MaxDYi/eElements/2.Firmware/eElements/Drivers/PWR/PWR.c

/*
 * @FilePath: \eElements\Drivers\PWR\PWR.c
 * @Author: MaxDYi
 * @Date: 2024-04-07 18:13:32
 * @LastEditors: MaxDYi
 * @LastEditTime: 2024-04-15 11:42:31
 * @Description:能耗管理相关的库函数
 */

#include "PWR.h"

 /**
  * @description: 关闭RTC唤醒定时器
  * @return {*}
  */
void PWR_CLK_Disable(void)
{
    RTC_HandleTypeDef RTCHandle;
    HAL_RTCEx_DeactivateWakeUpTimer(&RTCHandle);
}

/**
 * @description: 关闭GPIOA
 * @return {*}
 */
void PWR_DisableGPIOA(void) {
    __HAL_RCC_GPIOA_CLK_ENABLE();
    GPIO_InitTypeDef GPIO_InitStructure = { 0 };
    GPIO_InitStructure.Pin &= (~KEY_Pin);
    GPIO_InitStructure.Mode = GPIO_MODE_ANALOG;
    GPIO_InitStructure.Pull = GPIO_NOPULL;
    HAL_GPIO_Init(GPIOA , &GPIO_InitStructure);
    //__HAL_RCC_GPIOA_CLK_DISABLE();
}

/**
 * @description: 关闭GPIOB
 * @return {*}
 */
void PWR_DisableGPIOB(void) {
    __HAL_RCC_GPIOB_CLK_ENABLE();
    GPIO_InitTypeDef GPIO_InitStructure = { 0 };
    GPIO_InitStructure.Pin = GPIO_PIN_All;
    GPIO_InitStructure.Mode = GPIO_MODE_ANALOG;
    GPIO_InitStructure.Pull = GPIO_NOPULL;
    HAL_GPIO_Init(GPIOB , &GPIO_InitStructure);
    __HAL_RCC_GPIOB_CLK_DISABLE();
}

/**
 * @description: 关闭GPIOC
 * @return {*}
 */
void PWR_DisableGPIOC(void) {
    __HAL_RCC_GPIOC_CLK_ENABLE();
    GPIO_InitTypeDef GPIO_InitStructure = { 0 };
    GPIO_InitStructure.Pin &= (~PWR_LDO_Pin);
    GPIO_InitStructure.Mode = GPIO_MODE_ANALOG;
    GPIO_InitStructure.Pull = GPIO_NOPULL;
    HAL_GPIO_Init(GPIOC , &GPIO_InitStructure);
    //__HAL_RCC_GPIOC_CLK_DISABLE();
}

/**
 * @description: 关闭GPIOH
 * @return {*}
 */
void PWR_DisableGPIOH(void) {
    __HAL_RCC_GPIOH_CLK_ENABLE();
    GPIO_InitTypeDef GPIO_InitStructure = { 0 };
    GPIO_InitStructure.Pin = GPIO_PIN_All;
    GPIO_InitStructure.Mode = GPIO_MODE_ANALOG;
    GPIO_InitStructure.Pull = GPIO_NOPULL;
    HAL_GPIO_Init(GPIOA , &GPIO_InitStructure);
    __HAL_RCC_GPIOH_CLK_DISABLE();
}

/**
 * @description: 进入STOP2低功耗模式
 * @param {uint16_t} stopTime
 * @return {*}
 */
void PWR_EnterStop2Mode(uint16_t stopTime)
{
    HAL_SPI_DeInit(&hspi1);
    HAL_UART_DeInit(&huart1);
    HAL_ADC_DeInit(&hadc1);
    HAL_OPAMP_DeInit(&hopamp1);

    PWR_DisableGPIOA();
    PWR_DisableGPIOB();
    PWR_DisableGPIOC();
    PWR_DisableGPIOH();

    LED_GREEN_GPIO_Deinit();

    WKUP_Init();

    __HAL_RCC_PWR_CLK_ENABLE();
    __HAL_PWR_CLEAR_FLAG(PWR_FLAG_WU);
    __HAL_RCC_WAKEUPSTOP_CLK_CONFIG(RCC_STOP_WAKEUPCLOCK_MSI);
    HAL_RTCEx_DeactivateWakeUpTimer(&hrtc);
    HAL_RTCEx_SetWakeUpTimer_IT(&hrtc , stopTime , RTC_WAKEUPCLOCK_RTCCLK_DIV16);

    HAL_SuspendTick();

    HAL_PWREx_EnterSTOP2Mode(PWR_STOPENTRY_WFI);
}

/**
 * @description:退出STOP2低功耗模式
 * @return {*}
 */
void PWR_ExitStop2Mode(void)
{
    HAL_ResumeTick();
    SystemClock_Config();
    WKUP_Deinit();
    KEY_GPIO_Init();
    HAL_PWR_DisableWakeUpPin(PWR_WAKEUP_PIN4);
    MX_USART1_UART_Init();
    printf("WAKE UP\r\n");
    HAL_UART_DeInit(&huart1);
}

/**
 * @description: 判断电量充足
 * @return {*}
 */
uint8_t PWR_PowerEnough(void)
{
    if (Bat_GetVoltage() < BAT_LOW_VOLTAGE) {
        if (Bat_GetMode() == BAT_STATUS_CHARGING) {
            return TRUE;
        }
        else if (Bat_GetMode() == BAT_STATUS_FULL) {
            return TRUE;
        }
        else {
            return FALSE;
        }
    }
    return TRUE;
}
