MaxDYi/eElements/2.Firmware/eElements/Drivers/parameter/parameter.c

/*
 * @FilePath: \eElements\Drivers\parameter\parameter.c
 * @Author: MaxDYi
 * @Date: 2024-04-07 18:13:32
 * @LastEditors: MaxDYi
 * @LastEditTime: 2024-04-08 10:23:29
 * @Description:运行参数的存储与读取
 */
#include "parameter.h"

#define PARAMETER_ADDRESS 0x0803F800
#define PARAMETER_LEN 0x400

 /**
  * @description: Flash参数结构体
  * @return {*}
  */
struct parameters defaultParameters = {
    .initFlag = 0x01,
    .showStr = "Design by MaxDYi",
    .sleepTime = 30,
    .showFlag = {1, 1, 1, 1, 1, 1, 1, 1, 1, 1,
                 1, 1, 1, 1, 1, 1, 1, 1, 1, 1,
                 1, 1, 1, 1, 1, 1, 1, 1, 1, 1,
                 1, 1, 1, 1, 1, 1, 1, 1, 1, 1,
                 1, 1, 1, 1, 1, 1, 1, 1, 1, 1,
                 1, 1, 1, 1, 1, 1, 1, 1, 1, 1,
                 1, 1, 1, 1, 1, 1, 1, 1, 1, 1,
                 1, 1, 1, 1, 1, 1, 1, 1, 1, 1,
                 1, 1, 1, 1, 1, 1, 1, 1, 1, 1,
                 1, 1, 1, 1, 1, 1, 1, 1, 1, 1,
                 1, 1, 1, 1, 1, 1, 1, 1, 1, 1,
                 1, 1, 1, 1, 1, 1, 1, 1   }
};

/**
 * @description: 加载参数
 * @param {parameters*} para
 * @return {*}
 */
void LoadParameters(struct parameters* para)
{
    uint64_t readBuffer[PARAMETER_LEN / 8];
    uint32_t address = PARAMETER_ADDRESS;
    memset(readBuffer , 0xFF , sizeof(readBuffer));
    for (uint16_t i = 0; i < PARAMETER_LEN / 8; i++)
    {
        readBuffer[i] = (*(__IO uint64_t*)address);
        address = address + 8;
    }
    memcpy(para , readBuffer , sizeof(struct parameters));
    if (para->initFlag != 0x01)
    {
        memcpy(para , &defaultParameters , sizeof(struct parameters));
        SaveParameters(para);
    }
    else
    {
        memcpy(para , readBuffer , sizeof(struct parameters));
    }
}

/**
 * @description: 保存参数
 * @param {parameters*} para
 * @return {*}
 */
uint8_t SaveParameters(struct parameters* para)
{
    uint64_t writeBuffer[PARAMETER_LEN / 8];
    uint32_t address = PARAMETER_ADDRESS;
    static FLASH_EraseInitTypeDef EraseInitStruct;
    HAL_FLASH_Unlock();

    uint32_t SECTORError = 0;

    EraseInitStruct.TypeErase = FLASH_TYPEERASE_PAGES;
    EraseInitStruct.Banks = 0;
    EraseInitStruct.Page = 127;
    EraseInitStruct.NbPages = 1;


    if (HAL_FLASHEx_Erase(&EraseInitStruct , &SECTORError) != HAL_OK)
    {
        return -1;
    }
    memset(writeBuffer , 0xFF , sizeof(writeBuffer));
    memcpy(writeBuffer , para , sizeof(struct parameters));
    for (uint16_t i = 0; i < PARAMETER_LEN / 8; i++)
    {
        if (HAL_FLASH_Program(FLASH_TYPEPROGRAM_DOUBLEWORD , address , writeBuffer[i]) == HAL_OK)
        {
            address = address + 8;
        }
        else
        {
            return -1;
        }
    }
    HAL_FLASH_Lock();
    return 1;
}
